X-Illuminati/internet-of-spores/openscad/README.md

# EPD_1in9.scad
3D-model of the Waveshare 1.9 in. E-Paper Display
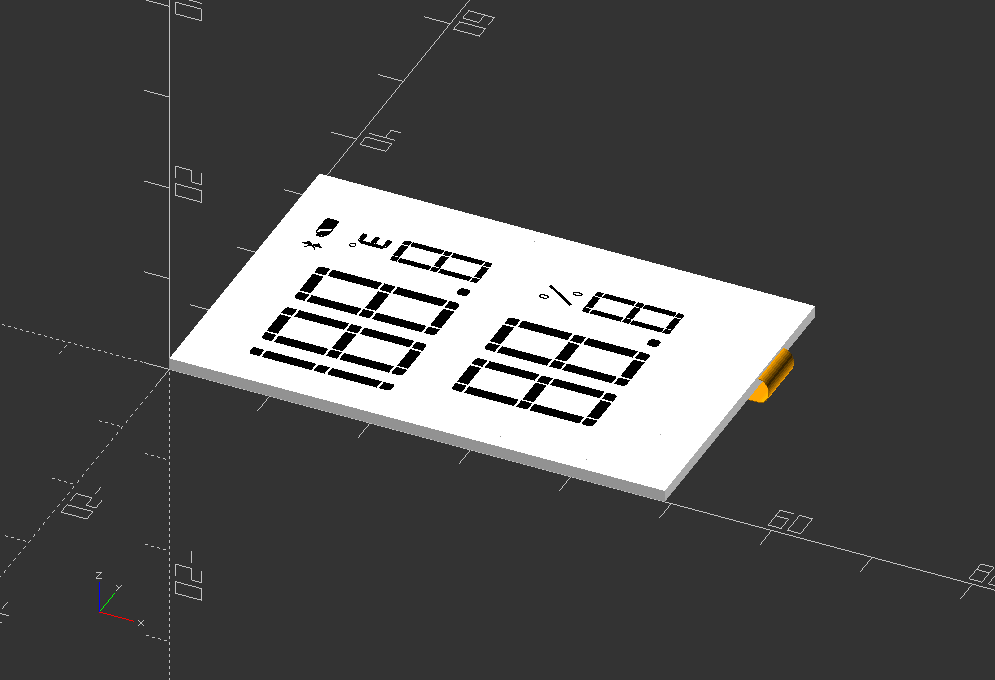
[picture p89: doc/renders/EPD_1in9_model.png]
Waveshare 1.9 in segmented E-Paper Display
