X-Illuminati/internet-of-spores/rtc_mem.cpp

#include "project_config.h"

#include <Arduino.h>
#include <Esp.h>

#include "connectivity.h"
#include "persistent.h"
#include "rtc_mem.h"


/* Global Data Structures */
uint32_t rtc_mem[RTC_MEM_MAX];


/* Function Prototypes */
static void refactor_timebase(void);


/* Functions */
// read rtc user memory and print some details to serial
// increments the boot count and returns true if the RTC memory was OK
bool load_rtc_memory(void)
{
  sleep_params_t *sleep_params = (sleep_params_t*) &rtc_mem[RTC_MEM_SLEEP_PARAMS];
  boot_count_t *boot_count = (boot_count_t*) &rtc_mem[RTC_MEM_BOOT_COUNT];
  bool retval = true;

  ESP.rtcUserMemoryRead(0, rtc_mem, sizeof(rtc_mem));
  if (rtc_mem[RTC_MEM_CHECK] + rtc_mem[RTC_MEM_BOOT_COUNT] != preinit_magic) {
    float tempf;
    int temp;
    Serial.println(String("Preinit magic doesn't compute, reinitializing (0x") + String(preinit_magic, HEX) + ")");
    invalidate_rtc();
    retval = false;

    tempf = persistent_read(PERSISTENT_TEMP_CALIB, DEFAULT_TEMP_CALIB);
    rtc_mem[RTC_MEM_TEMP_CAL] = *((uint32_t*)&tempf);
    tempf = persistent_read(PERSISTENT_HUMIDITY_CALIB, DEFAULT_HUMIDITY_CALIB);
    rtc_mem[RTC_MEM_HUMIDITY_CAL] = *((uint32_t*)&tempf);
    tempf = persistent_read(PERSISTENT_BATTERY_CALIB, DEFAULT_BATTERY_CALIB);
    rtc_mem[RTC_MEM_BATTERY_CAL] = *((uint32_t*)&tempf);

    temp = persistent_read(PERSISTENT_HIGH_WATER_SLOT, DEFAULT_HIGH_WATER_SLOT);
    if (temp <= 0)
      temp = 1;
    if (temp > NUM_STORAGE_SLOTS)
      temp = NUM_STORAGE_SLOTS;
    sleep_params->high_water_slot = temp;

    temp = persistent_read(PERSISTENT_SLEEP_TIME_MS, (int)DEFAULT_SLEEP_TIME_MS);
    if (temp < 200)
      temp = 200;
    if (temp > MAX_ESP_SLEEP_TIME_MS)
      temp = MAX_ESP_SLEEP_TIME_MS;
    sleep_params->sleep_time_ms = temp;
  }
  boot_count->boot_count++;

  Serial.printf("[%llu] ", uptime());
  Serial.print("setup: reset reason=");
  Serial.print(ESP.getResetReason());
  Serial.print(", boot count=");
  Serial.print(boot_count->boot_count);

#if EXTRA_DEBUG
  {
    flags_time_t *flags = (flags_time_t*) &rtc_mem[RTC_MEM_FLAGS_TIME];
    Serial.print(", epd refr=");
    Serial.print(boot_count->epd_partial_refresh_count);
    Serial.print(", flags=0x");
    Serial.print((uint8_t)flags->flags, HEX);
    Serial.print(", connect failures=");
    Serial.print((uint8_t)flags->fail_count);
  }
#endif

  Serial.print(", num readings=");
  Serial.println(rtc_mem[RTC_MEM_NUM_READINGS]);

#if EXTRA_DEBUG
  {
    float* rtc_float_ptr;
    Serial.printf("[%llu] ", uptime());
    Serial.print("RTC_SIZE=");
    Serial.print(RTC_MEM_MAX);
    Serial.print(", temp cal=");
    rtc_float_ptr = (float*)&rtc_mem[RTC_MEM_TEMP_CAL];
    Serial.print(*rtc_float_ptr);
    Serial.print(", humidity cal=");
    rtc_float_ptr = (float*)&rtc_mem[RTC_MEM_HUMIDITY_CAL];
    Serial.print(*rtc_float_ptr);
    Serial.print(", battery cal=");
    rtc_float_ptr = (float*)&rtc_mem[RTC_MEM_BATTERY_CAL];
    Serial.print(*rtc_float_ptr);
    Serial.print(", sleep time=");
    Serial.print(sleep_params->sleep_time_ms);
    Serial.print(", high water=");
    Serial.print(sleep_params->high_water_slot);

    Serial.println();
  }
#endif

  if (RTC_MEM_MAX > 128)
    Serial.println("*************************\nWARNING RTC_MEM_MAX > 128\n*************************");

  return retval;
}

// clear/reinitialize rtc memory
void invalidate_rtc(void)
{
  flags_time_t *timestruct = (flags_time_t*) &rtc_mem[RTC_MEM_FLAGS_TIME];
  uint16_t clock_cal;

  memset(rtc_mem, 0, sizeof(rtc_mem));
  ESP.rtcUserMemoryWrite(0, rtc_mem, sizeof(rtc_mem));

  clock_cal = persistent_read(PERSISTENT_CLOCK_CALIB, DEFAULT_SLEEP_CLOCK_ADJ);
  if (clock_cal > 0)
    timestruct->clock_cal = clock_cal;
  else
    timestruct->clock_cal = DEFAULT_SLEEP_CLOCK_ADJ;
}

// return the uptime in ms (added to the RTC stored time)
uint64_t uptime(void)
{
  uint64_t uptime_ms;
  flags_time_t *timestruct = (flags_time_t*) &rtc_mem[RTC_MEM_FLAGS_TIME];

  // boot timestamp + current millis()
  uptime_ms = timestruct->millis;
  uptime_ms += millis();
  return uptime_ms;
}

// helper for saving rtc memory
void save_rtc(uint64_t sleep_time_us)
{
  flags_time_t *timestruct = (flags_time_t*) &rtc_mem[RTC_MEM_FLAGS_TIME];
  uint64_t backup_millis = timestruct->millis; //store the current uptime value in case we aren't sleeping

  // update the stored millis including some overhead for the write, suspend, and wake
  timestruct->millis += millis() + sleep_time_us/1000 + timestruct->clock_cal;

  // update the header checksum
  rtc_mem[RTC_MEM_CHECK] = preinit_magic - rtc_mem[RTC_MEM_BOOT_COUNT];

  // store the array to RTC memory
  ESP.rtcUserMemoryWrite(0, rtc_mem, sizeof(rtc_mem));

  // restore the old uptime in case we aren't sleeping (millis won't be reset in that case)
  timestruct->millis = backup_millis;
}

// helper for saving rtc memory before entering deep sleep
void deep_sleep(uint64_t time_us)
{
  flags_time_t *timestruct = (flags_time_t*) &rtc_mem[RTC_MEM_FLAGS_TIME];

  if (time_us > (MAX_ESP_SLEEP_TIME_MS*1000))
    time_us = (MAX_ESP_SLEEP_TIME_MS*1000);

  save_rtc(time_us);

#if TETHERED_MODE
  ESP.deepSleepInstant(time_us, RF_NO_CAL);
#else
  if (0 != (timestruct->flags & FLAG_BIT_CONNECT_NEXT_WAKE))
    ESP.deepSleepInstant(time_us, RF_NO_CAL); //we want to be able to connect on next boot
  else
    ESP.deepSleepInstant(time_us, RF_DISABLED);
#endif
}

// store sensor reading in the rtc mem ring buffer
void store_reading(sensor_type_t type, int32_t val)
{
  sensor_reading_t *reading;
  int slot;

  // determine the next free slot in the RTC memory ring buffer
  slot = rtc_mem[RTC_MEM_FIRST_READING] + rtc_mem[RTC_MEM_NUM_READINGS];
  if (slot >= NUM_STORAGE_SLOTS)
    slot -= NUM_STORAGE_SLOTS;

  // update the ring buffer metadata
  if (rtc_mem[RTC_MEM_NUM_READINGS] == NUM_STORAGE_SLOTS) {
    rtc_mem[RTC_MEM_FIRST_READING]++;
    if (rtc_mem[RTC_MEM_FIRST_READING] >= NUM_STORAGE_SLOTS)
      rtc_mem[RTC_MEM_FIRST_READING]=0;
    refactor_timebase();
  } else {
    rtc_mem[RTC_MEM_NUM_READINGS]++;
  }

  // store the sensor reading in RTC memory at the given slot
  reading = (sensor_reading_t*) &rtc_mem[RTC_MEM_DATA+slot*NUM_WORDS(sensor_reading_t)];
  reading->type = type;
  reading->value = val;
}

// reset the rtc mem ring buffer
void clear_readings(unsigned int num /*defaults to NUM_STORAGE_SLOTS*/)
{
  if (num >= rtc_mem[RTC_MEM_NUM_READINGS]) {
    // simple case - just reset the ring buffer
    rtc_mem[RTC_MEM_FIRST_READING]=0;
    rtc_mem[RTC_MEM_NUM_READINGS]=0;
  } else {
    // increment first reading to "erase" num readings
    rtc_mem[RTC_MEM_FIRST_READING] += num;
    if (rtc_mem[RTC_MEM_FIRST_READING] >= NUM_STORAGE_SLOTS)
      rtc_mem[RTC_MEM_FIRST_READING] -= NUM_STORAGE_SLOTS;

    rtc_mem[RTC_MEM_NUM_READINGS] -= num;
  }

  refactor_timebase();
}

// print the stored pressure readings from the rtc mem ring buffer
void dump_readings(void)
{
#if (EXTRA_DEBUG != 0)
  flags_time_t timestamp = {0,0,0,0};
  const char typestrings[8][12] = {
    "UNKNOWN",
    "TEMP (C)",
    "HUMI (%)",
    "PRES (kPa)",
    "1.0um (/cf)",
    "2.5um (/cf)",
    "BATT (V)",
    "TIME (ms)",
  };
  char formatted[47];
  formatted[46]=0;

  Serial.println("slot | type        |      rawvalue");
  Serial.println("-----+-------------+--------------");


  for (unsigned i=0; i < rtc_mem[RTC_MEM_NUM_READINGS]; i++) {
    sensor_reading_t *reading;
    const char* type = typestrings[0];
    int slot;

    // find the slot indexed into the ring buffer
    slot = rtc_mem[RTC_MEM_FIRST_READING] + i;
    if (slot >= NUM_STORAGE_SLOTS)
      slot -= NUM_STORAGE_SLOTS;

    reading = (sensor_reading_t*) &rtc_mem[RTC_MEM_DATA+slot*NUM_WORDS(sensor_reading_t)];

    // determine the sensor type
    switch(reading->type) {
      case SENSOR_TEMPERATURE:
        type=typestrings[1];
      break;

      case SENSOR_HUMIDITY:
        type=typestrings[2];
      break;

      case SENSOR_PRESSURE:
        type=typestrings[3];
      break;

      case SENSOR_PARTICLE_1_0:
        type=typestrings[4];
      break;

      case SENSOR_PARTICLE_2_5:
        type=typestrings[5];
      break;

      case SENSOR_BATTERY_VOLTAGE:
        type=typestrings[6];
      break;

      case SENSOR_TIMESTAMP_OFFS:
        type=typestrings[7];
        timestamp.millis = (rtc_mem[RTC_MEM_DATA_TIMEBASE] << RTC_DATA_TIMEBASE_SHIFT) + (uint64_t)reading->value;
      break;

      case SENSOR_UNKNOWN:
      default:
        type=typestrings[0];
      break;
    }

    // format an output row with the slot, type, and data
    if (reading->type == SENSOR_TIMESTAMP_OFFS)
      snprintf(formatted, 45, "%4u | %-11s | %13llu", i, type, timestamp.millis);
    else if ((reading->type == SENSOR_PARTICLE_1_0)
          || (reading->type == SENSOR_PARTICLE_2_5))
      snprintf(formatted, 45, "%4u | %-11s | %13llu", i, type, ((uint64_t)reading->value)*1000ULL);
    else
      snprintf(formatted, 45, "%4u | %-11s | %+13.3f", i, type, reading->value/1000.0);
    Serial.println(formatted);
  }
  Serial.printf("[%llu] dump complete\n", uptime());
#endif
}

// helper for resetting the time offset for all of the
// SENSOR_TIMESTAMP_OFFS in the rtc mem ring buffer
static void refactor_timebase(void)
{
  uint64_t oldbase = rtc_mem[RTC_MEM_DATA_TIMEBASE] << RTC_DATA_TIMEBASE_SHIFT;
  uint64_t newbase = 0;

  // iterate through each reading in the rtc mem ring buffer
  for (unsigned i=0; i < rtc_mem[RTC_MEM_NUM_READINGS]; i++) {
    sensor_reading_t *reading;
    int slot;

    // find the slot indexed into the ring buffer
    slot = rtc_mem[RTC_MEM_FIRST_READING] + i;
    if (slot >= NUM_STORAGE_SLOTS)
      slot -= NUM_STORAGE_SLOTS;

    reading = (sensor_reading_t*) &rtc_mem[RTC_MEM_DATA+slot*NUM_WORDS(sensor_reading_t)];

    // we only care about timestamp offsets
    if (reading->type == SENSOR_TIMESTAMP_OFFS) {
      uint64_t timestamp;
      timestamp = oldbase + (uint64_t)reading->value;

      // special case for the first timestamp offset we find:
      // use it as the new base timestamp that all of the others will
      // be an offset from
      if (0 == newbase)
        newbase = timestamp & RTC_DATA_TIMEBASE_MASK;

      // cast the timestamp from the old base offset to the new one
      reading->value = (int32_t)(timestamp - newbase);
    }
  }

  // special case when no timestamp sensor readings were found:
  // keep a relatively current value for future readings to use
  // as their base offset
  if (0 == newbase)
    newbase = uptime() & RTC_DATA_TIMEBASE_MASK;

  // store the new timebase
  rtc_mem[RTC_MEM_DATA_TIMEBASE] = (uint32_t)(newbase >> RTC_DATA_TIMEBASE_SHIFT);
}
